rn-t/MicroNaos_open/firmware/Core/Inc/tools.hpp

#ifndef INC_TOOLS_HPP_
#define INC_TOOLS_HPP_

#include "main.h"
#include "arm_math.h"
#include "mazelibrary.hpp"

namespace tools{
    uint8_t get_rotated_wall(uint8_t direction, uint8_t wall);
    int16_t direction_to_deg(uint8_t direction);
    int16_t deg_sub(int16_t a, int16_t b);
    int16_t deg_normalize(int16_t a);
    float32_t deg_normalize(float32_t a);
}

#endif
