rn-t/MicroNaos_open/firmware/Core/Src/tools.cpp

#include "tools.hpp"
/**
 * @brief マウスから見た壁と向きを入力することで、迷路情報に準じた(y軸正方向を向いていると仮定した)壁の情報を返す。
*/
uint8_t tools::get_rotated_wall(uint8_t direction, uint8_t wall){
    uint8_t out = 0;
    switch (direction){
        case Direction::up:
            out = wall;
            break;
        case Direction::left:
            if ((wall & Direction::up) == Direction::up){
                out += Direction::left;
            }
            if ((wall & Direction::left) == Direction::left){
                out += Direction::down;
            }
            if ((wall & Direction::down) == Direction::down){
                out += Direction::right;
            }
            if ((wall & Direction::right) == Direction::right){
                out += Direction::up;
            }
            break;
        case Direction::down:
            if ((wall & Direction::up) == Direction::up){
                out += Direction::down;
            }
            if ((wall & Direction::left) == Direction::left){
                out += Direction::right;
            }
            if ((wall & Direction::down) == Direction::down){
                out += Direction::up;
            }
            if ((wall & Direction::right) == Direction::right){
                out += Direction::left;
            }
            break;
        case Direction::right:
            if ((wall & Direction::up) == Direction::up){
                out += Direction::right;
            }
            if ((wall & Direction::left) == Direction::left){
                out += Direction::up;
            }
            if ((wall & Direction::down) == Direction::down){
                out += Direction::left;
            }
            if ((wall & Direction::right) == Direction::right){
                out += Direction::down;
            }
            break;
    }
    return out;
}

int16_t tools::direction_to_deg(uint8_t direction){
    uint16_t out = 0;
    switch(direction){
            case Direction::up:
                out = 0;
                break;
            case Direction::down:
                out = 180;
                break;
            case Direction::left:
                out = 90;
                break;
            case Direction::right:
                out = -90;
                break;
        }
    return out;
}

int16_t tools::deg_sub(int16_t a, int16_t b){
    int16_t out = a - b;
    return deg_normalize(out);
}

int16_t tools::deg_normalize(int16_t a){
    int16_t out = a;
    while(out <= -180 || 180 < out){
        if(out <= -180){
            out += 360;
        }else if(180 < out){
            out -= 360;
        }
    }
    return out;

}

float32_t tools::deg_normalize(float32_t a){
    float32_t out = a;
    while(out <= -180.0f || 180.0f < out){
        if(out <= -180.0f){
            out += 360.0f;
        }else if(180.0f < out){
            out -= 360.0f;
        }
    }
    return out;

}
